slepcat/Mule-CNC-2.0/STL&NC/Y01-2 belt lock.stl

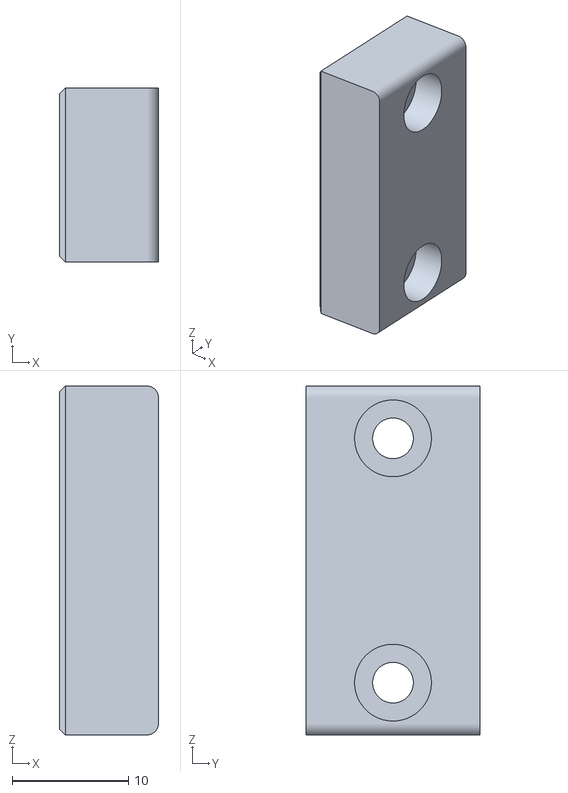
[picture p18: CAD file, 2014-09-08]
STL&NC/Y01-2 belt lock.stl
8.50 x 15.0 x 30.0
