slepcat/Mule-CNC-2.0/STL&NC/U001-3 spacer.stl

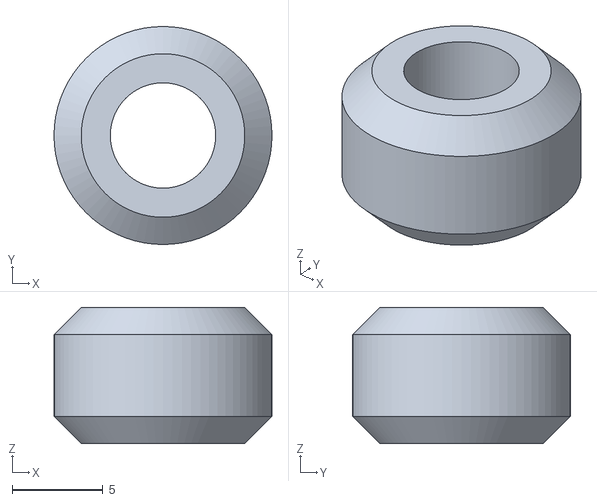
[picture p19: CAD file, 2014-09-08]
STL&NC/U001-3 spacer.stl
12.0 x 12.0 x 7.51
