slepcat/Mule-CNC-2.0/STL&NC/tinyg case power.stl

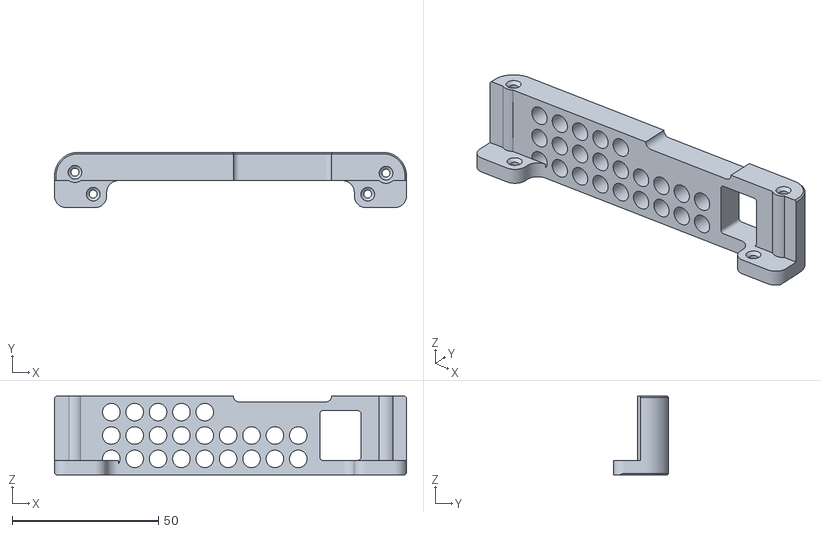
[picture p20: CAD file, 2014-09-08]
STL&NC/tinyg case power.stl
120.5 x 18.9 x 27.0
