slepcat/Mule-CNC-2.0/STL&NC/accesory bracket left.stl

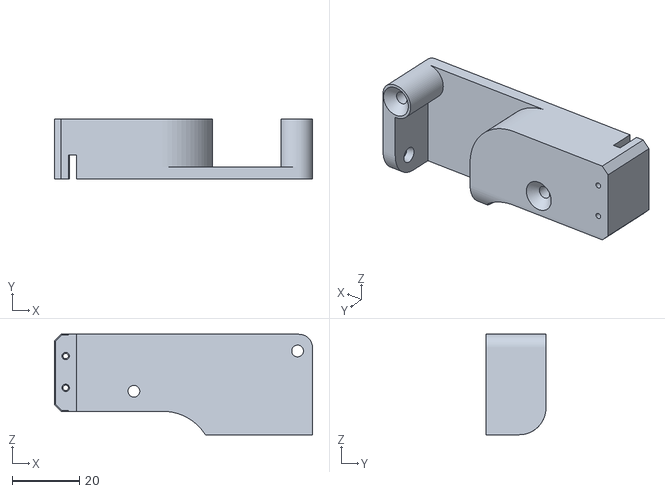
[picture p21: CAD file, 2014-09-08]
STL&NC/accesory bracket left.stl
77.0 x 17.9 x 30.0
