slepcat/Mule-CNC-2.0/STL&NC/plate.stl

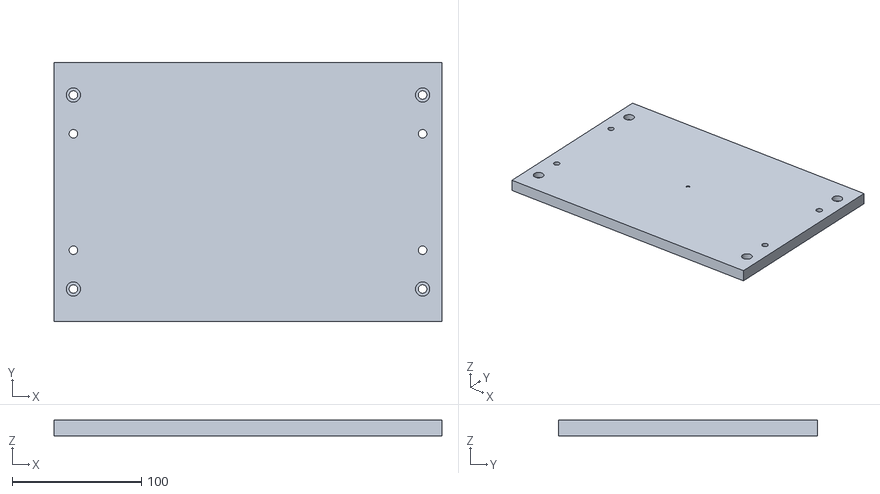
[picture p22: CAD file, 2014-09-08]
STL&NC/plate.stl
300.0 x 200.0 x 12.0
