slepcat/Mule-CNC-2.0/STL&NC/X005-3 belt lock.stl

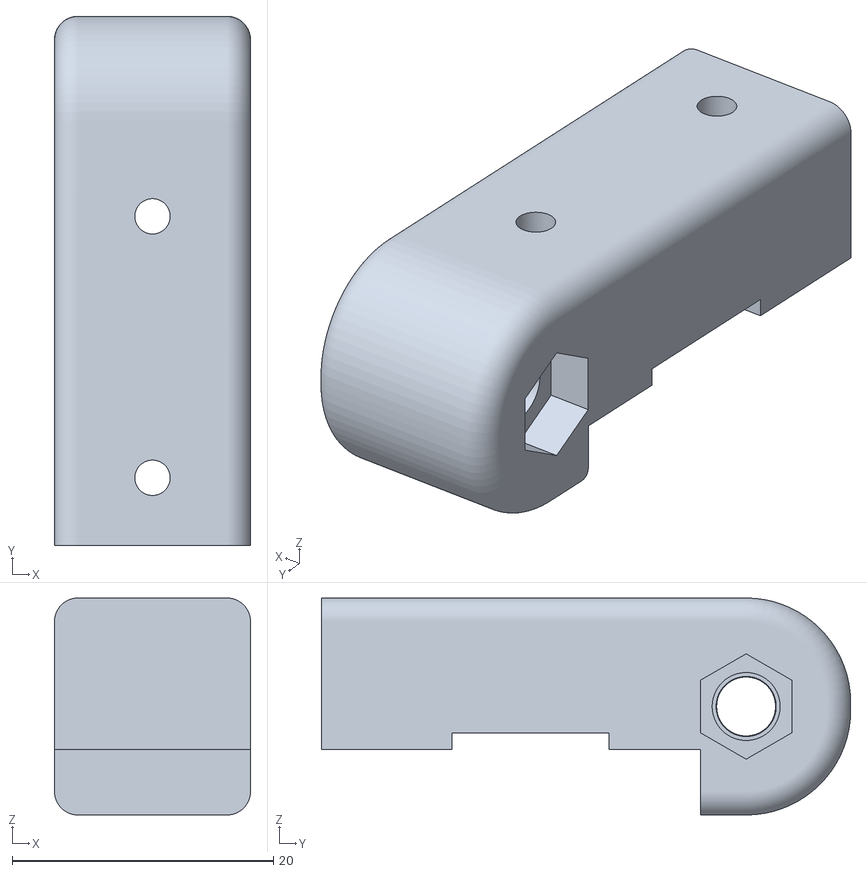
[picture p23: CAD file, 2014-09-08]
STL&NC/X005-3 belt lock.stl
15.0 x 40.5 x 16.6
