slepcat/Mule-CNC-2.0/STL&NC/X005 left bracket.stl

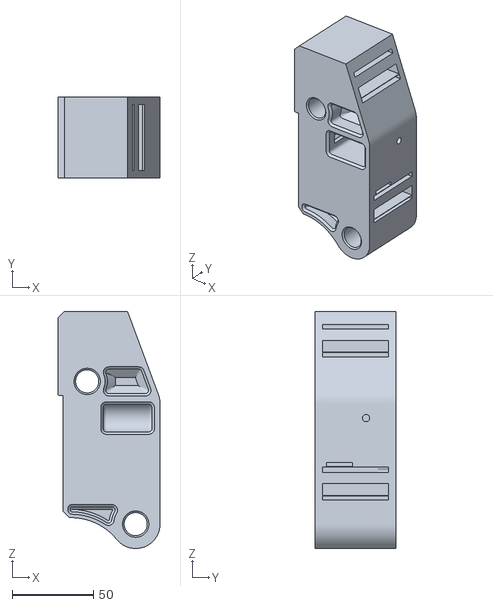
[picture p24: CAD file, 2014-07-26]
STL&NC/X005 left bracket.stl
62.9 x 50.0 x 145.9
