slepcat/Mule-CNC-2.0/STL&NC/X003 right bracket.stl

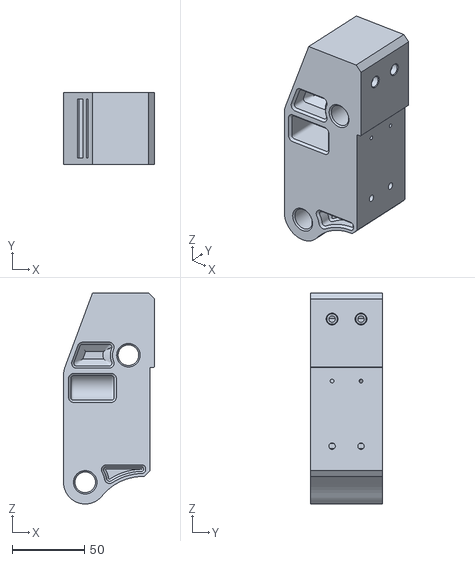
[picture p25: CAD file, 2014-07-26]
STL&NC/X003 right bracket.stl
62.9 x 50.0 x 145.9
