slepcat/Mule-CNC-2.0/STL&NC/Y001 y motor mount.stl

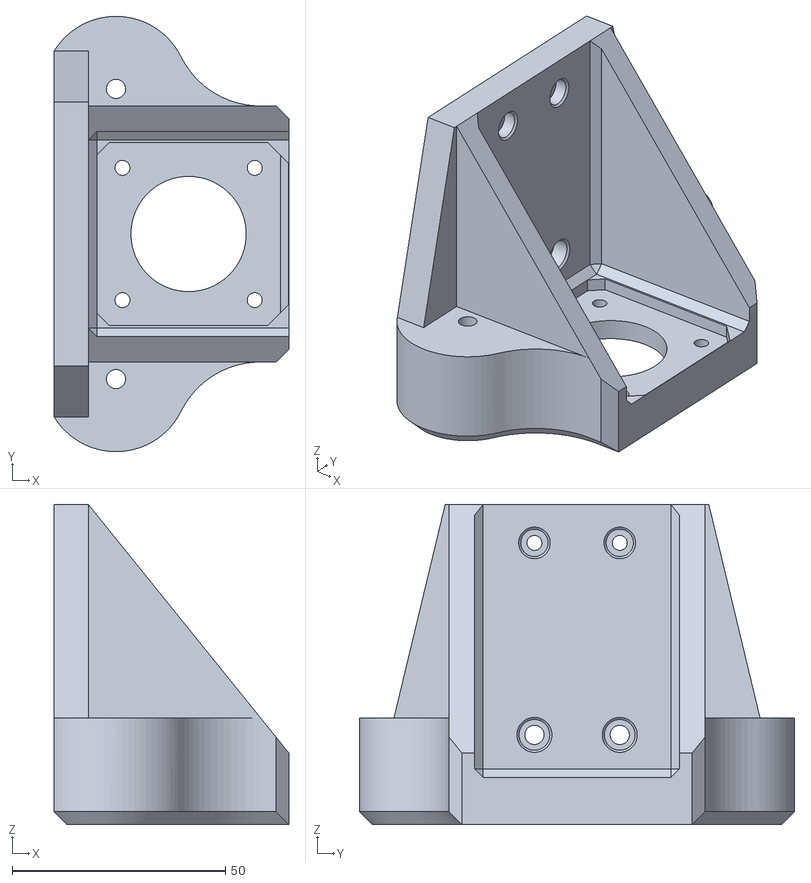
[picture p26: CAD file, 2014-07-23]
STL&NC/Y001 y motor mount.stl
55.0 x 102.0 x 75.0
