slepcat/Mule-CNC-2.0/STL&NC/Y001-1 belt lock.stl

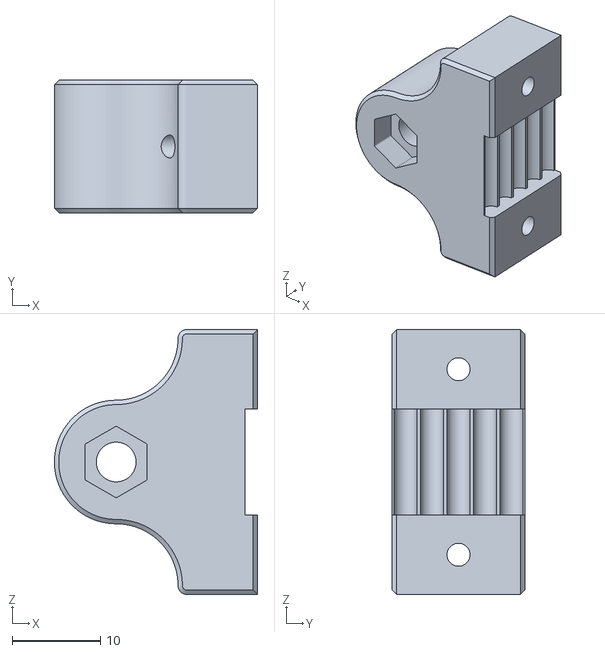
[picture p27: CAD file, 2014-07-23]
STL&NC/Y001-1 belt lock.stl
23.0 x 15.0 x 30.0
