slepcat/Mule-CNC-2.0/STL&NC/X007 right bracket.stl

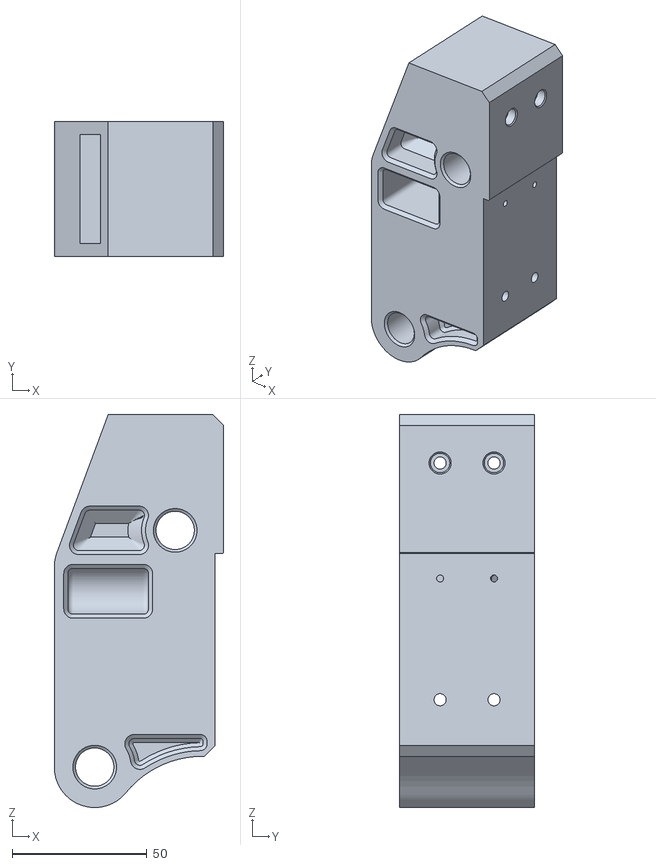
[picture p28: CAD file, 2014-07-23]
STL&NC/X007 right bracket.stl
62.9 x 50.0 x 145.8
