slepcat/Mule-CNC-2.0/STL&NC/Z001-3 spacer.stl

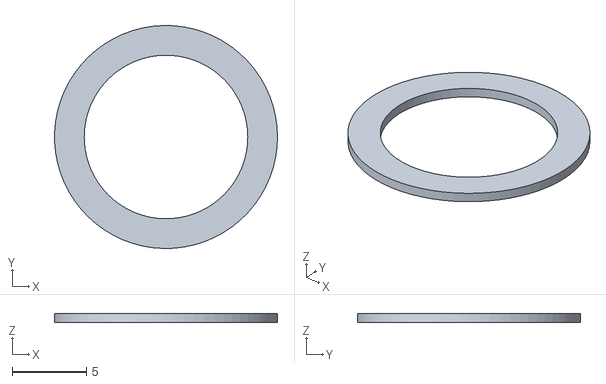
[picture p29: CAD file, 2014-07-07]
STL&NC/Z001-3 spacer.stl
15.0 x 15.0 x 0.6
