slepcat/Mule-CNC-2.0/STL&NC/Z001 z carriage.stl

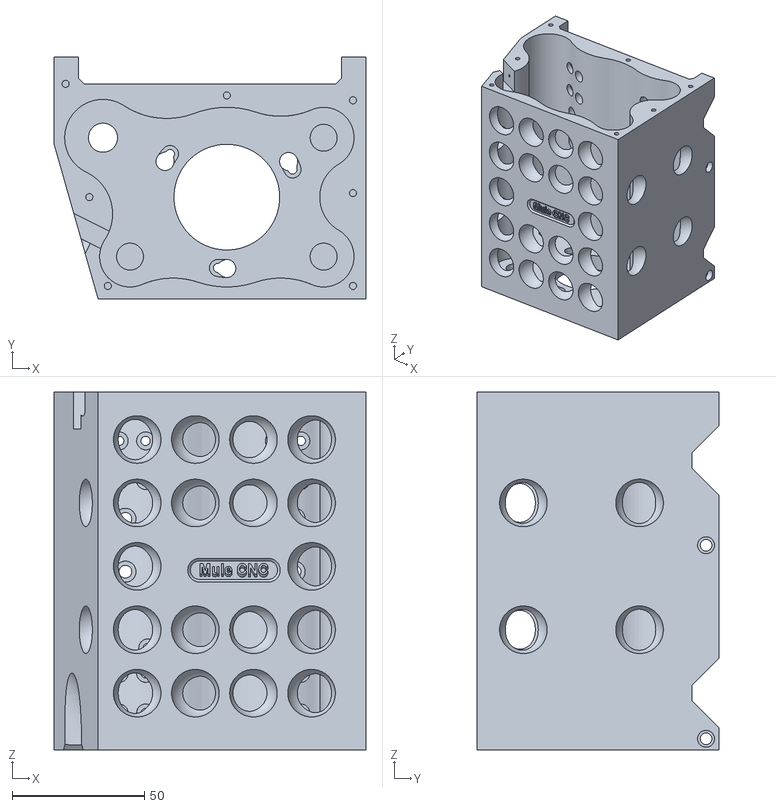
[picture p30: CAD file, 2014-07-07]
STL&NC/Z001 z carriage.stl
118.0 x 91.5 x 135.5
