slepcat/Mule-CNC-2.0/STL&NC/Z003 cover.stl

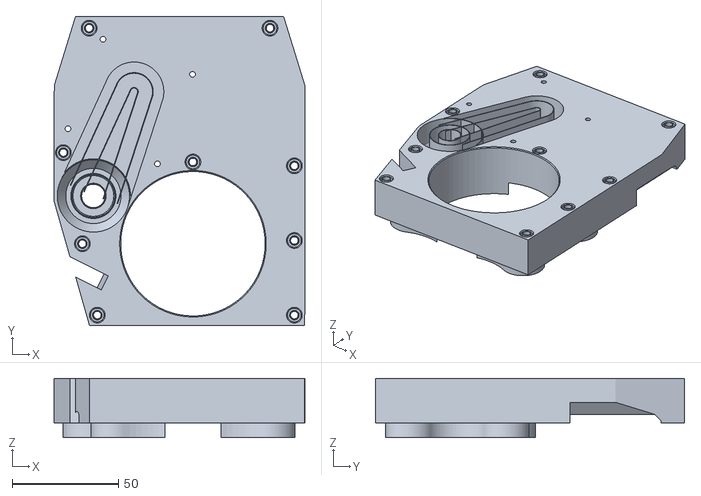
[picture p31: CAD file, 2014-07-07]
STL&NC/Z003 cover.stl
118.1 x 145.5 x 28.0
