slepcat/Mule-CNC-2.0/STL&NC/Z001-4 coller.stl

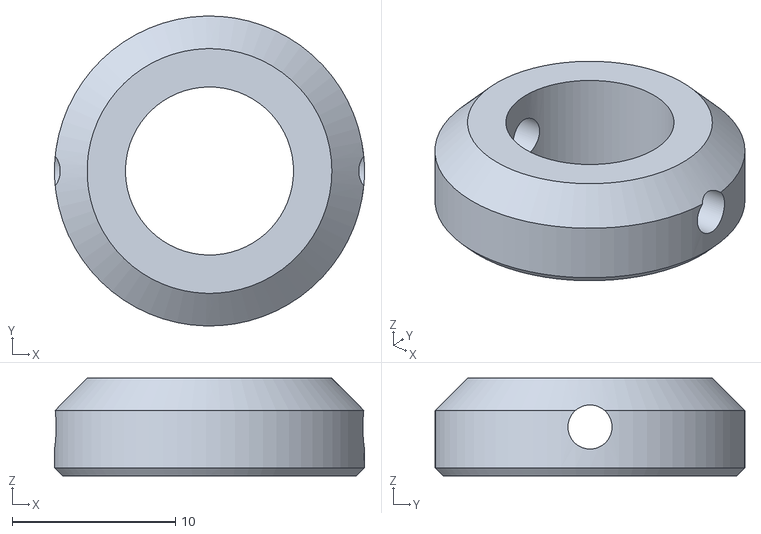
[picture p32: CAD file, 2014-07-07]
STL&NC/Z001-4 coller.stl
19.0 x 19.0 x 6.00
