slepcat/Mule-CNC-2.0/STL&NC/Z006 dust skirt.stl

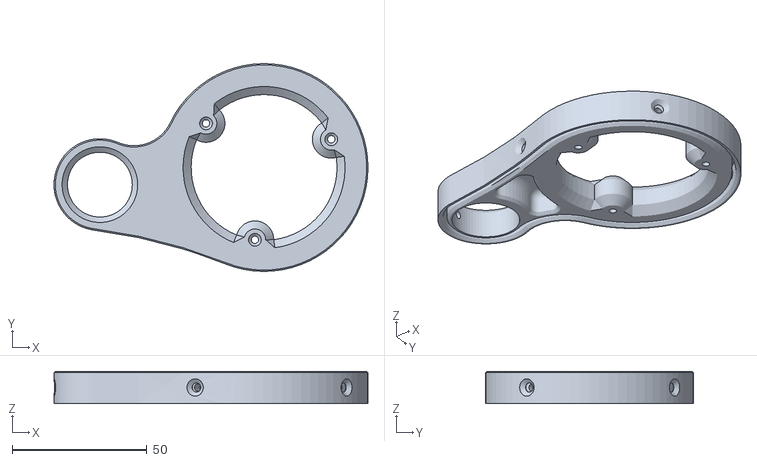
[picture p33: CAD file, 2014-07-07]
STL&NC/Z006 dust skirt.stl
116.3 x 77.0 x 12.0
