slepcat/Mule-CNC-2.0/STL&NC/Z005 z motor housing.stl

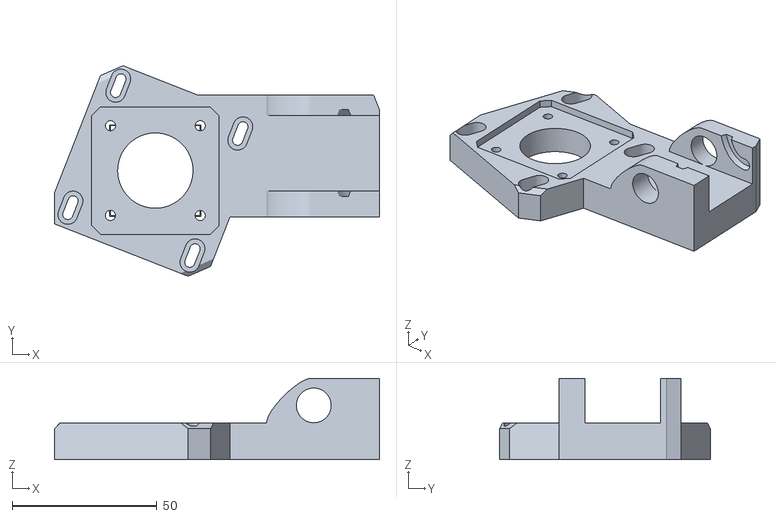
[picture p34: CAD file, 2014-07-07]
STL&NC/Z005 z motor housing.stl
112.2 x 72.7 x 28.0
