slepcat/Mule-CNC-2.0/STL&NC/U001-2 spacer.stl

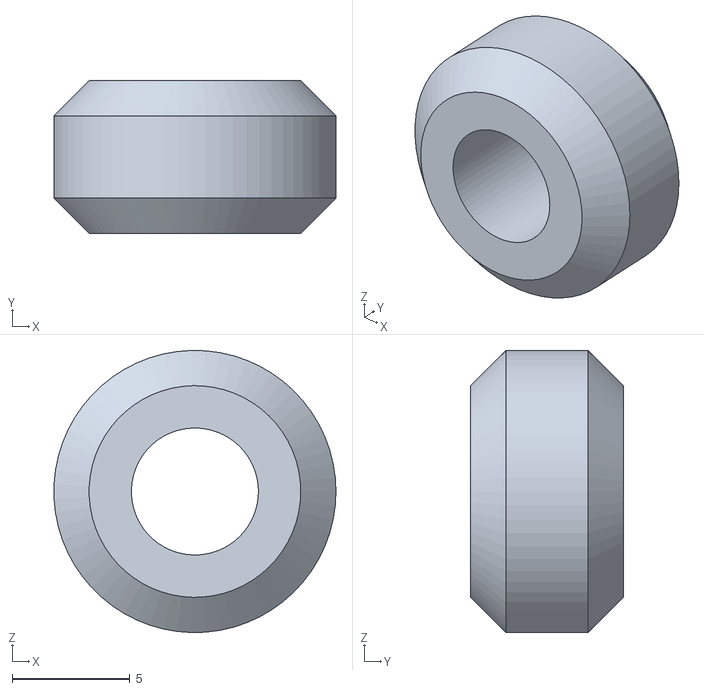
[picture p35: CAD file, 2014-07-03]
STL&NC/U001-2 spacer.stl
12.0 x 6.50 x 12.0
