slepcat/Mule-CNC-2.0/STL&NC/U001 smooth idler.stl

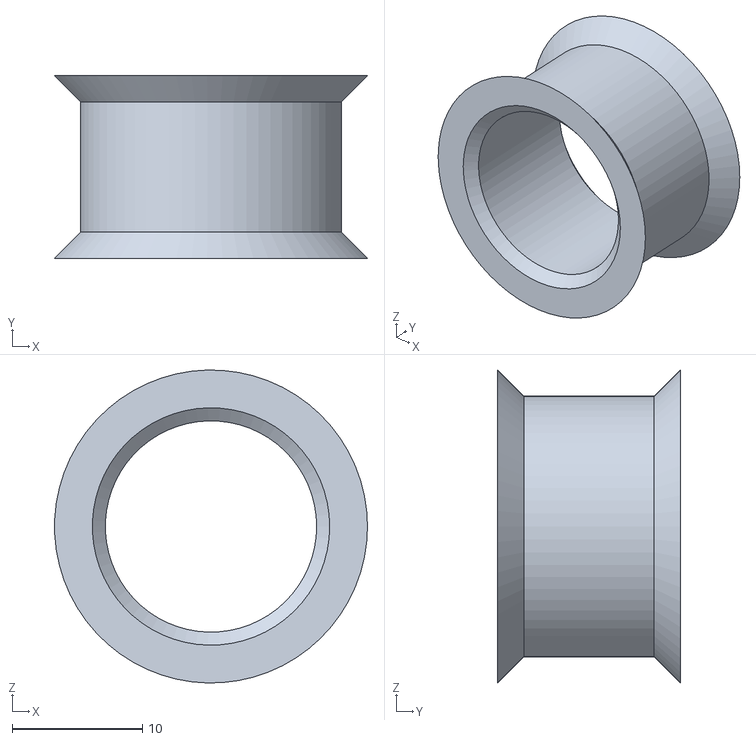
[picture p36: CAD file, 2014-06-29]
STL&NC/U001 smooth idler.stl
24.0 x 14.0 x 24.0
