slepcat/Mule-CNC-2.0/STL&NC/X001 motor housing.stl

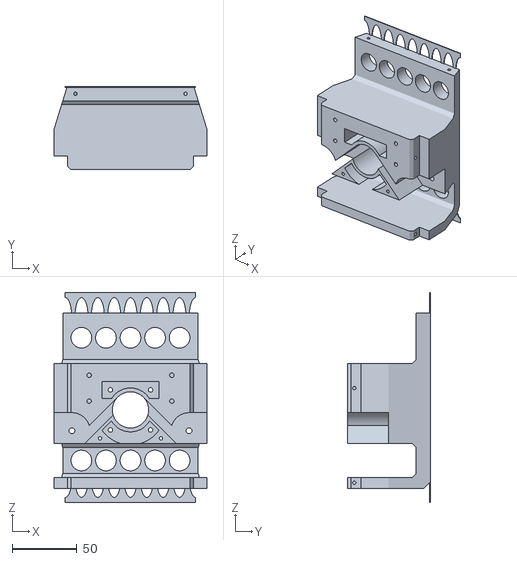
[picture p37: CAD file, 2014-06-29]
STL&NC/X001 motor housing.stl
118.0 x 64.0 x 162.5
