slepcat/Mule-CNC-2.0/STL&NC/S001 dc housing.stl

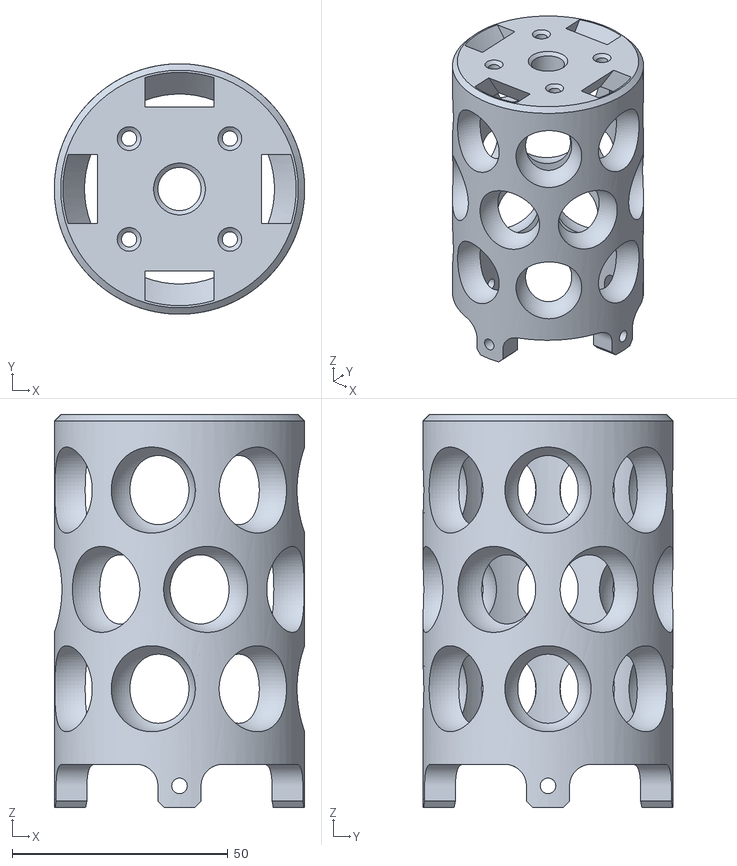
[picture p38: CAD file, 2014-06-24]
STL&NC/S001 dc housing.stl
58.0 x 58.0 x 91.0
