slepcat/Mule-CNC-2.0/Test/S004 silencer heat test.csv

Temp(Celsius): 25 | Time(Second): 0
Temp(Celsius): 24 | Time(Second): 1
Temp(Celsius): 24 | Time(Second): 2
Temp(Celsius): 24 | Time(Second): 3
Temp(Celsius): 24 | Time(Second): 4
Temp(Celsius): 24 | Time(Second): 5
Temp(Celsius): 24 | Time(Second): 6
Temp(Celsius): 24 | Time(Second): 7
Temp(Celsius): 24 | Time(Second): 8
Temp(Celsius): 24 | Time(Second): 9
Temp(Celsius): 24 | Time(Second): 10
Temp(Celsius): 24 | Time(Second): 11
Temp(Celsius): 24 | Time(Second): 12
Temp(Celsius): 24 | Time(Second): 13
Temp(Celsius): 24 | Time(Second): 14
Temp(Celsius): 25 | Time(Second): 15
Temp(Celsius): 24 | Time(Second): 16
Temp(Celsius): 24 | Time(Second): 17
Temp(Celsius): 24 | Time(Second): 18
Temp(Celsius): 24 | Time(Second): 19
Temp(Celsius): 24 | Time(Second): 20
Temp(Celsius): 24 | Time(Second): 21
Temp(Celsius): 25 | Time(Second): 22
Temp(Celsius): 24 | Time(Second): 23
Temp(Celsius): 24 | Time(Second): 24
Temp(Celsius): 24 | Time(Second): 25
Temp(Celsius): 24 | Time(Second): 26
Temp(Celsius): 24 | Time(Second): 27
Temp(Celsius): 24 | Time(Second): 28
Temp(Celsius): 24 | Time(Second): 29
Temp(Celsius): 25 | Time(Second): 30
Temp(Celsius): 24 | Time(Second): 31
Temp(Celsius): 24 | Time(Second): 32
Temp(Celsius): 24 | Time(Second): 33
Temp(Celsius): 24 | Time(Second): 34
Temp(Celsius): 24 | Time(Second): 35
Temp(Celsius): 24 | Time(Second): 36
Temp(Celsius): 24 | Time(Second): 37
Temp(Celsius): 24 | Time(Second): 38
Temp(Celsius): 25 | Time(Second): 39
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
Temp(Celsius): 29 | Time(Second): 515
Temp(Celsius): 29 | Time(Second): 516
Temp(Celsius): 29 | Time(Second): 517
Temp(Celsius): 29 | Time(Second): 518
Temp(Celsius): 29 | Time(Second): 519
Temp(Celsius): 29 | Time(Second): 520
Temp(Celsius): 29 | Time(Second): 521
